tomcircuit/rcl57mcu/hardware/rcl57_mcu/output/ti57mcu_v2_bot3d.png

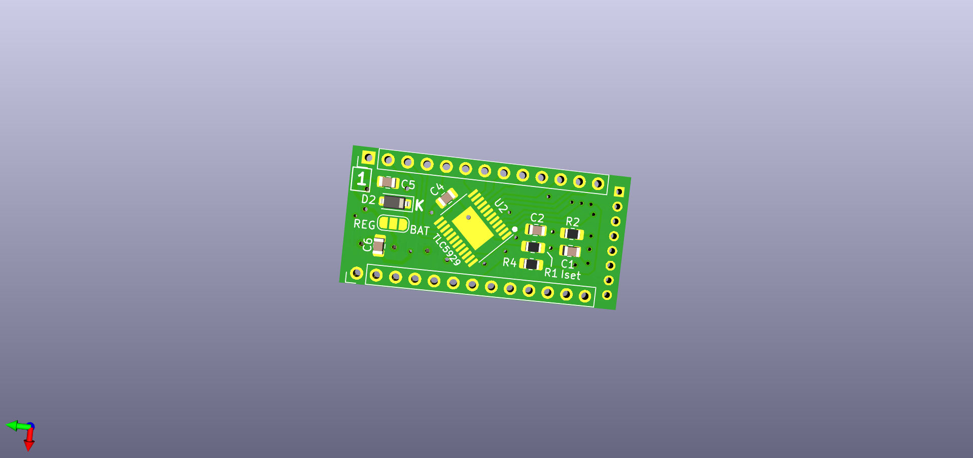
hardware/rcl57_mcu/output/ti57mcu_v2_bot3d.png
