tomcircuit/rcl57mcu/media/column input w 1K8 pulldown segment B.png

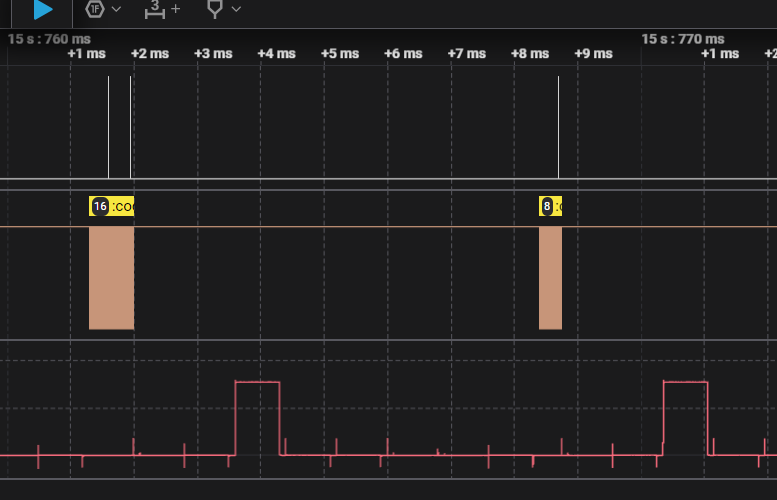
media/column input w 1K8 pulldown segment B.png
