tomcircuit/rcl57mcu/media/column input w 1K8 pulldown segment P.png

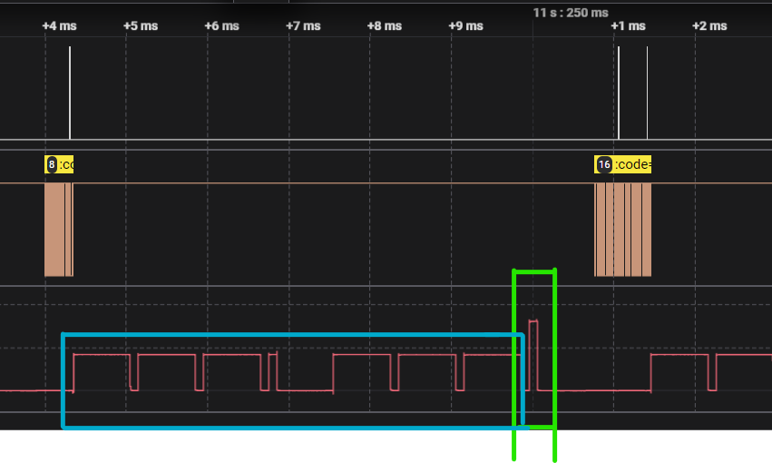
media/column input w 1K8 pulldown segment P.png
