tomcircuit/rcl57mcu/media/connected_segment_pulse.png

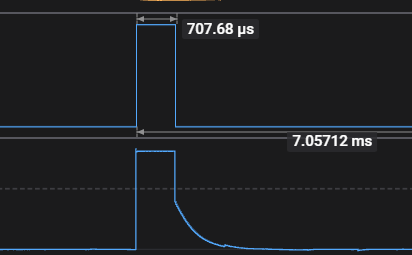
media/connected_segment_pulse.png
