tomcircuit/rcl57mcu/media/first_STM32_emulation_saleae.png

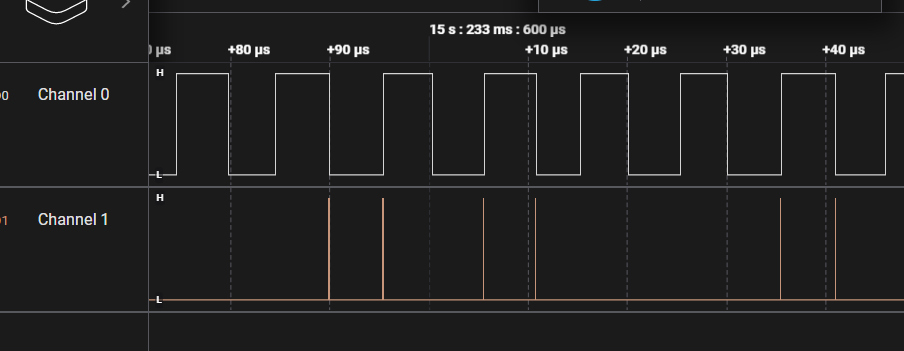
media/first_STM32_emulation_saleae.png
