tomcircuit/rcl57mcu/media/open_segment_pulse.png

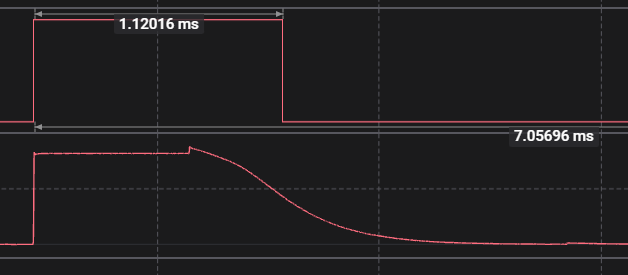
media/open_segment_pulse.png
