tomcircuit/rcl57mcu/media/overlap segments.png

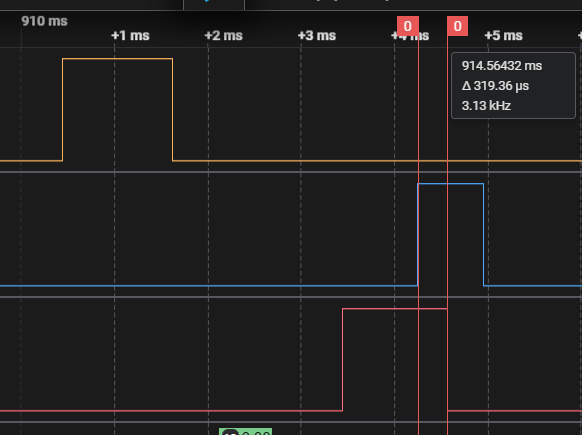
media/overlap segments.png
