tomcircuit/rcl57mcu/media/prototype hack.jpg

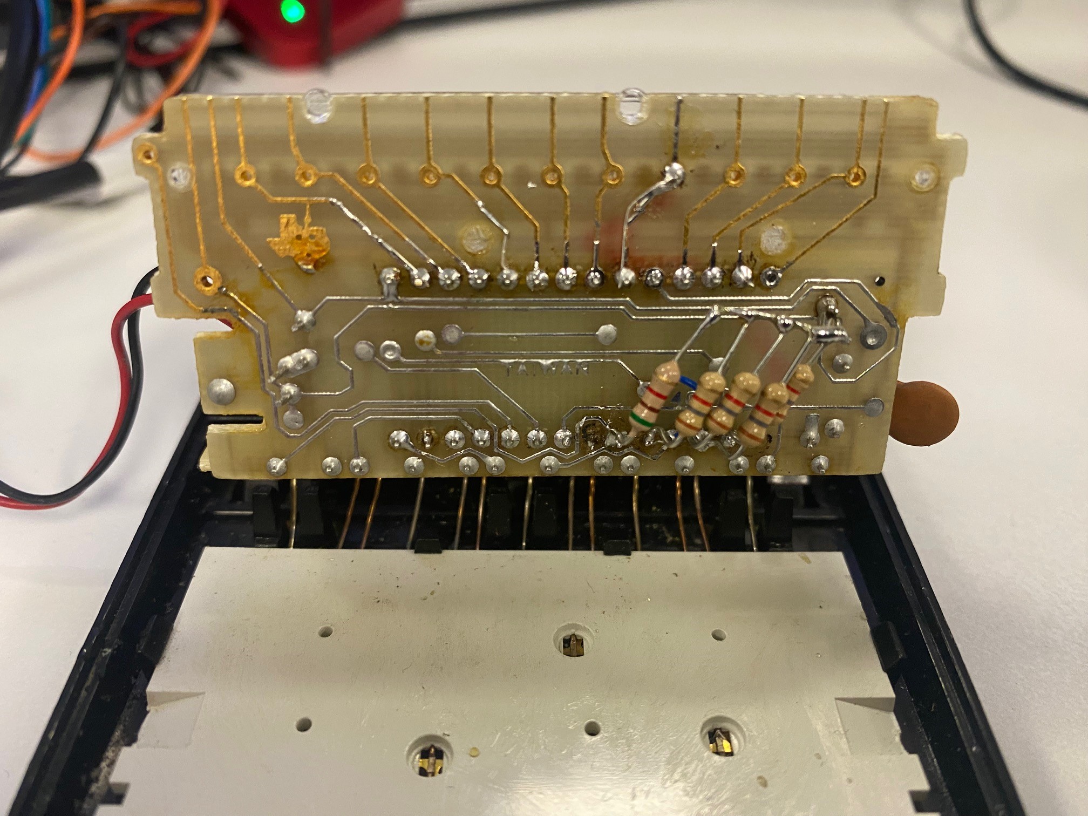
media/prototype hack.jpg
