tomcircuit/rcl57mcu/media/assembled debug board.jpg

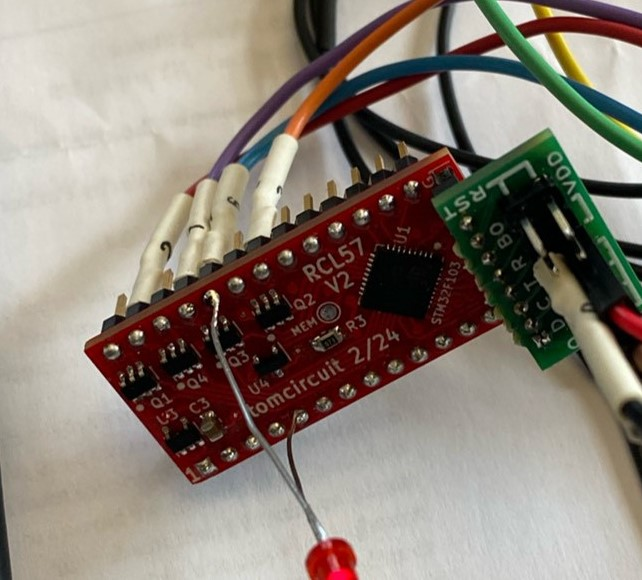
media/assembled debug board.jpg
