tomcircuit/rcl57mcu/hardware/rcl57_mcu/release/fab01/ti57mcu__v1_Assembly.pdf

R Dd10 | +3V3 1 | v tomcircuit CSWCLK | x12 T w10 v1 2024 TMS+ SWDIO | GND | d13 G Q2 U1 C3 Q1 U93 Q4 U96 | U92 D1 U98

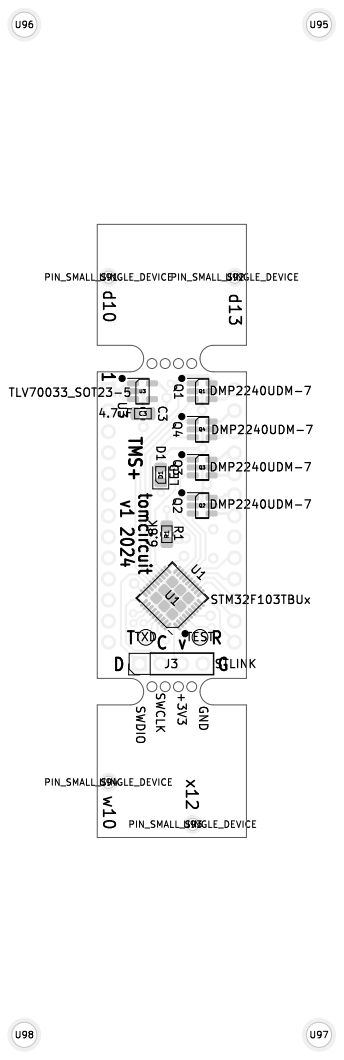
[picture p17: page 1]

Id: 1/1 Title: File: ti57mcu.kicad_pcb Sheet:

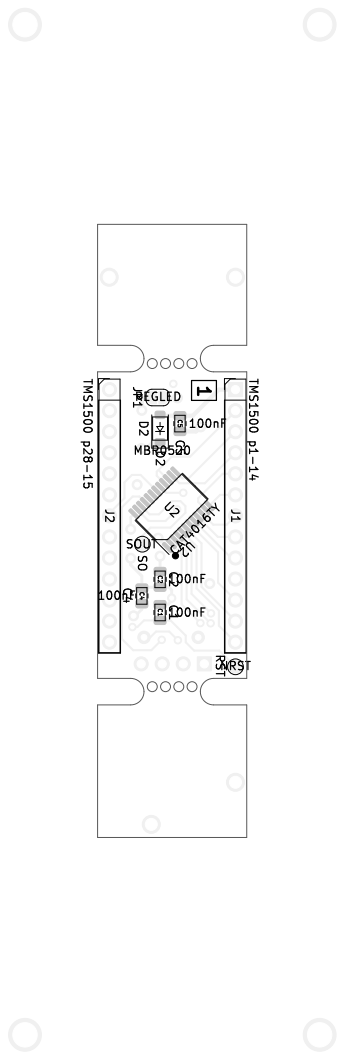
[picture p18: page 2]
Id: 1/1 Title: File: ti57mcu.kicad_pcb Sheet: C²; 100nF MBR0520 D²; 100nF REGLED

1 SO RST C2 D2C5 JP1 C4 U2 C1 1 2 3 4 5 6 1 2 3 4 5 6 ABCD ABCD Date: KiCad E.D.A. kicad 7.0.8 Size: A4 Rev:
