tomcircuit/rcl57mcu/hardware/rcl57_mcu/output/rcl57_mcu_bot_assy.pdf

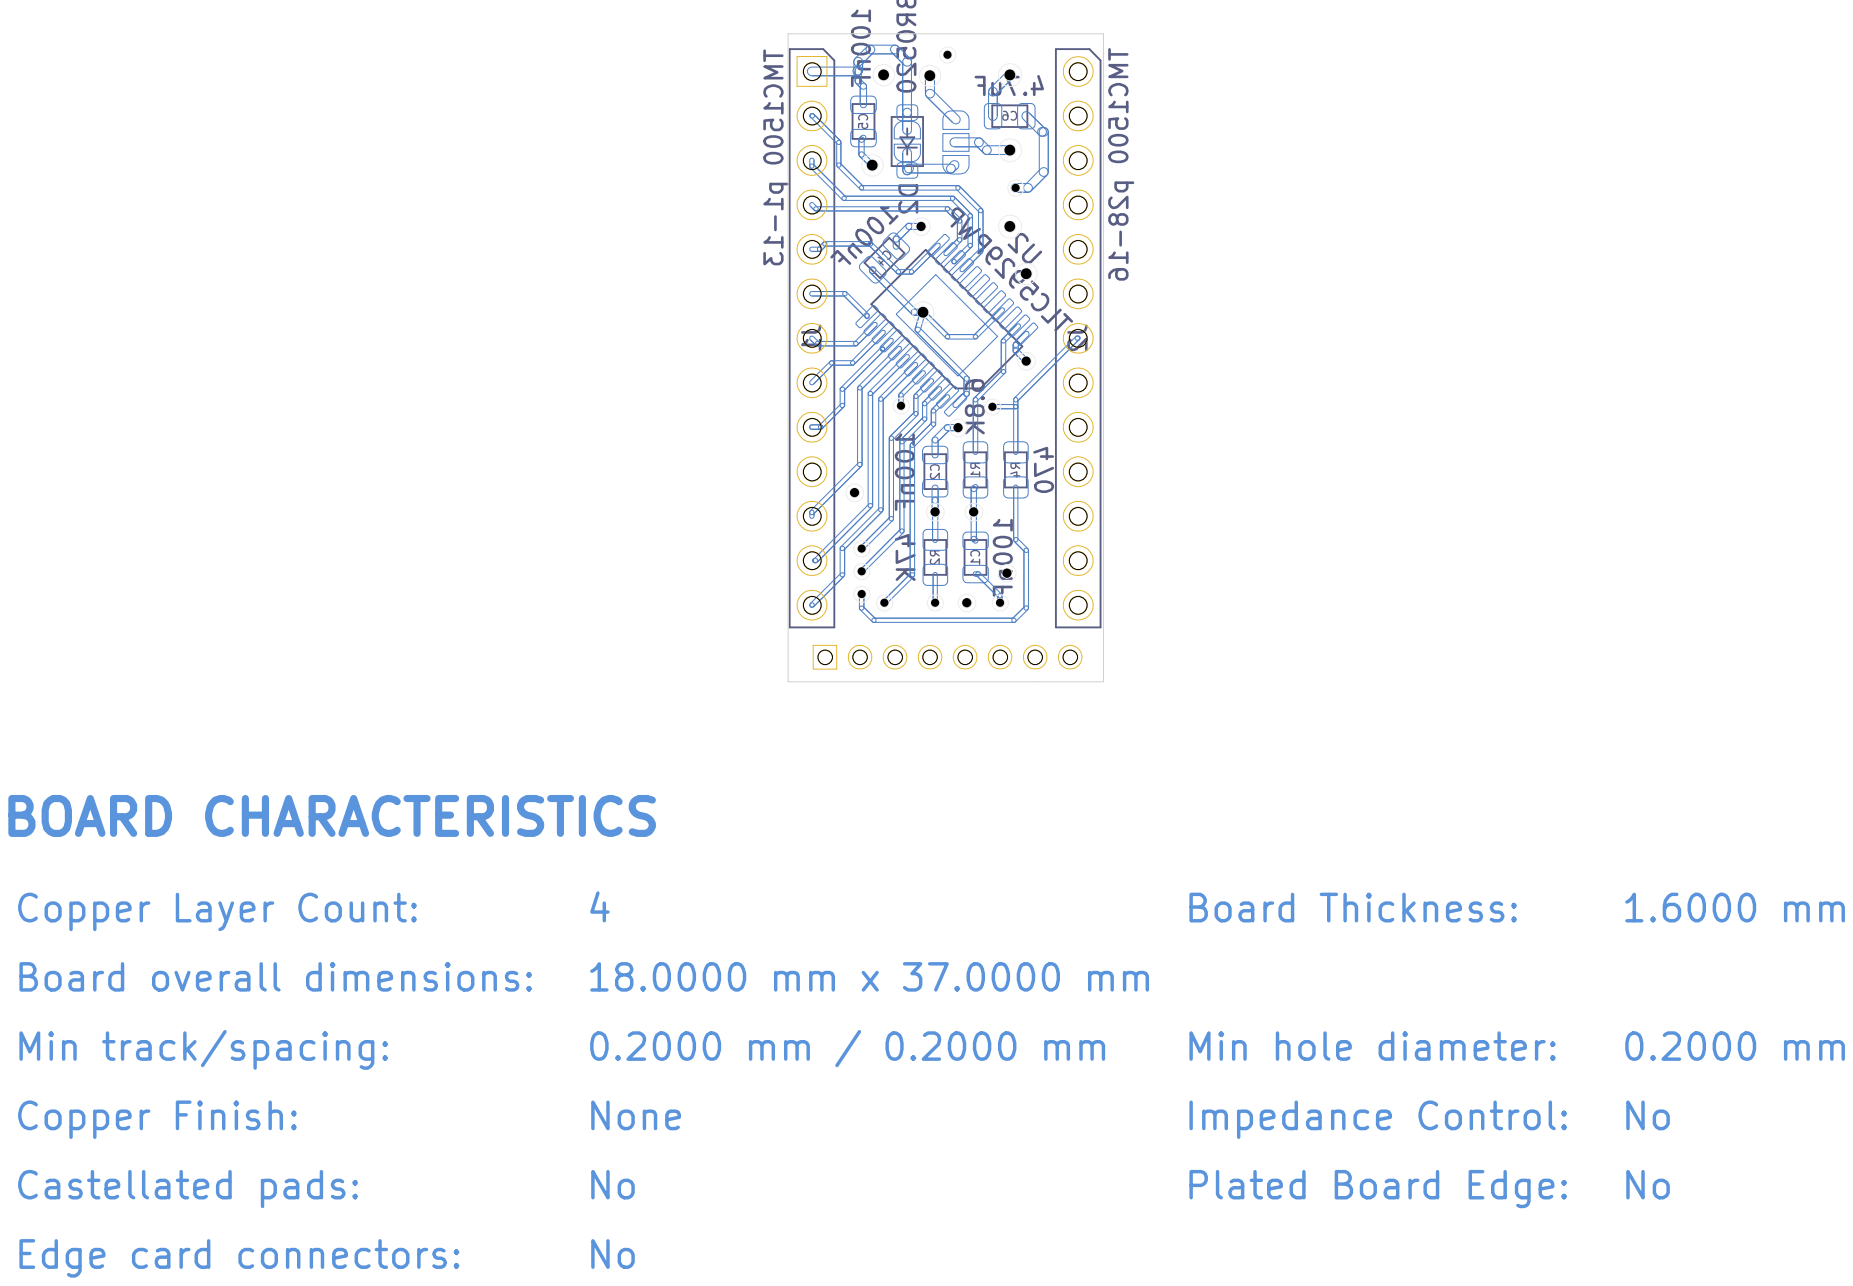
[picture p32: page 1]
