tomcircuit/rcl57mcu/hardware/rcl57_mcu/output/rcl57_mcu_schematic.pdf

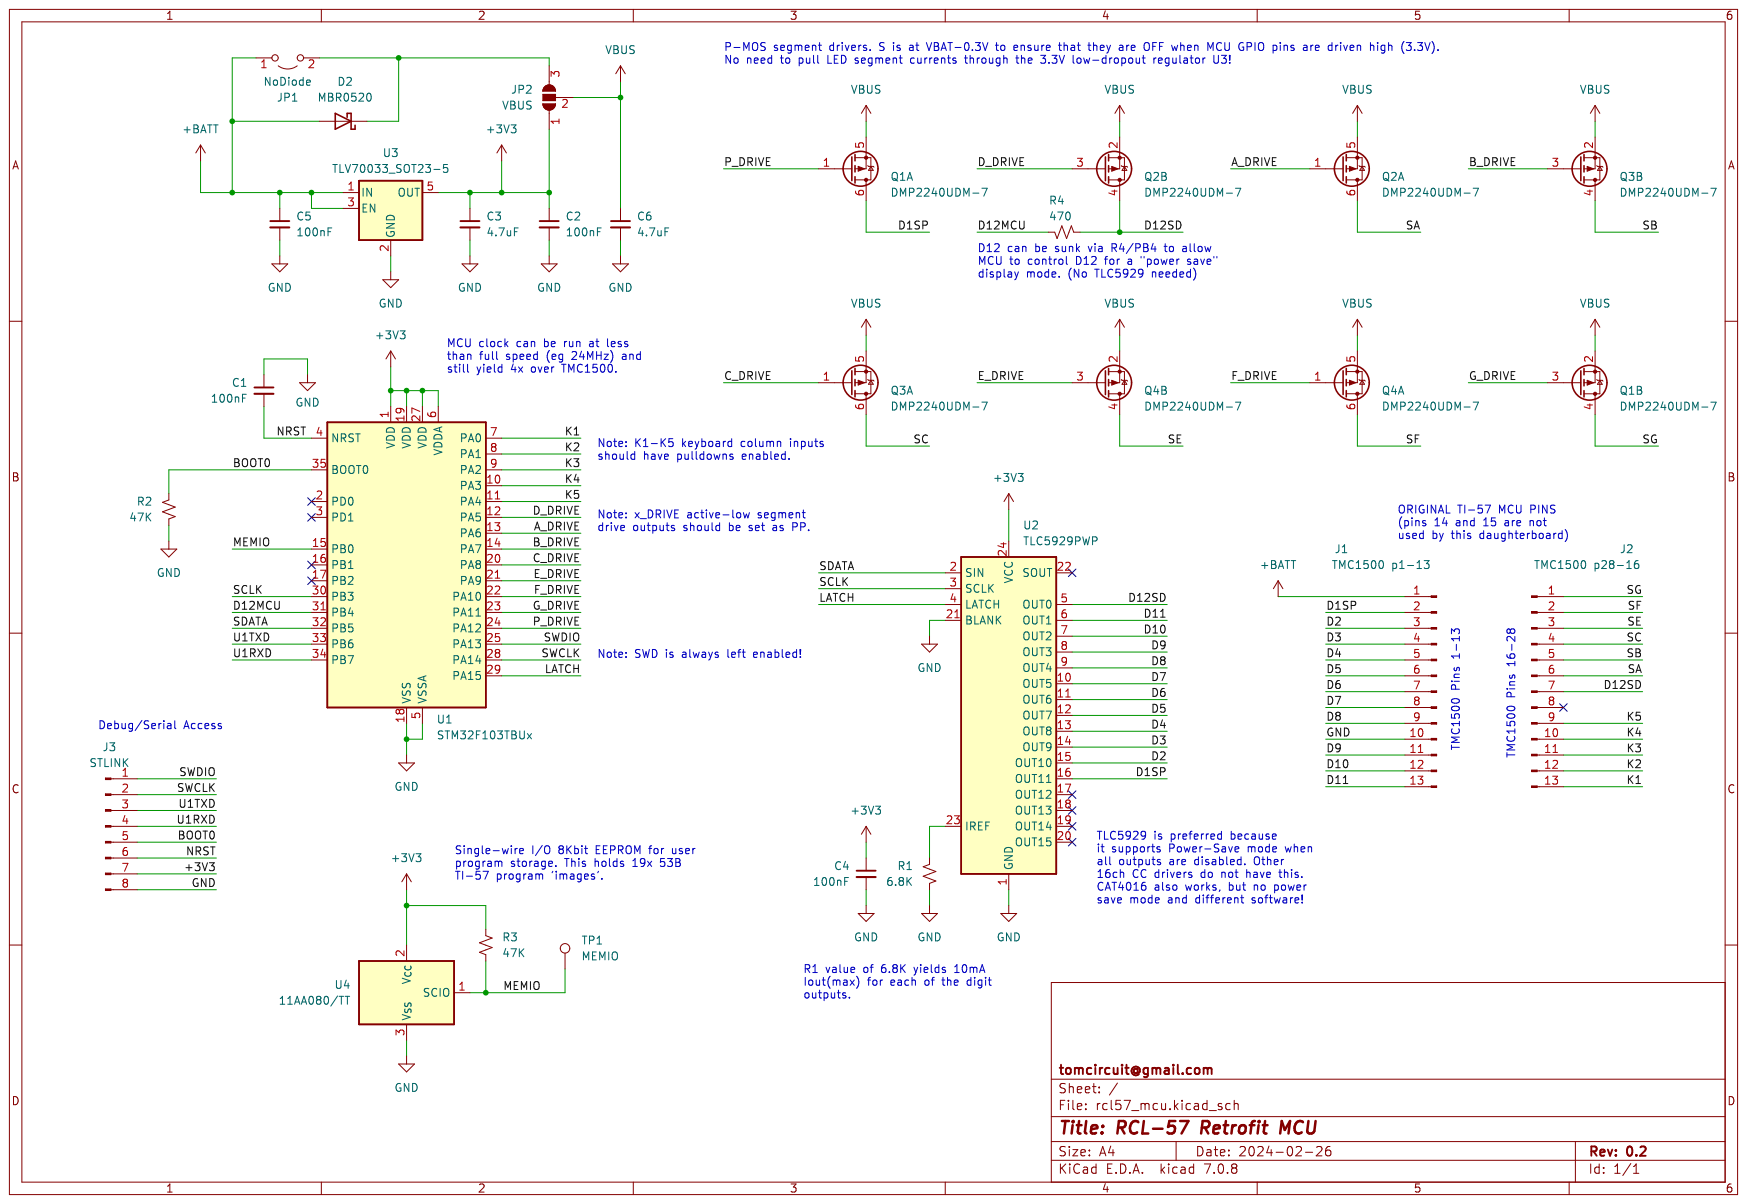
[picture p33: page 1]
