tomcircuit/rcl57mcu/hardware/rcl57_mcu/output/rcl57_mcu_top_assy.pdf

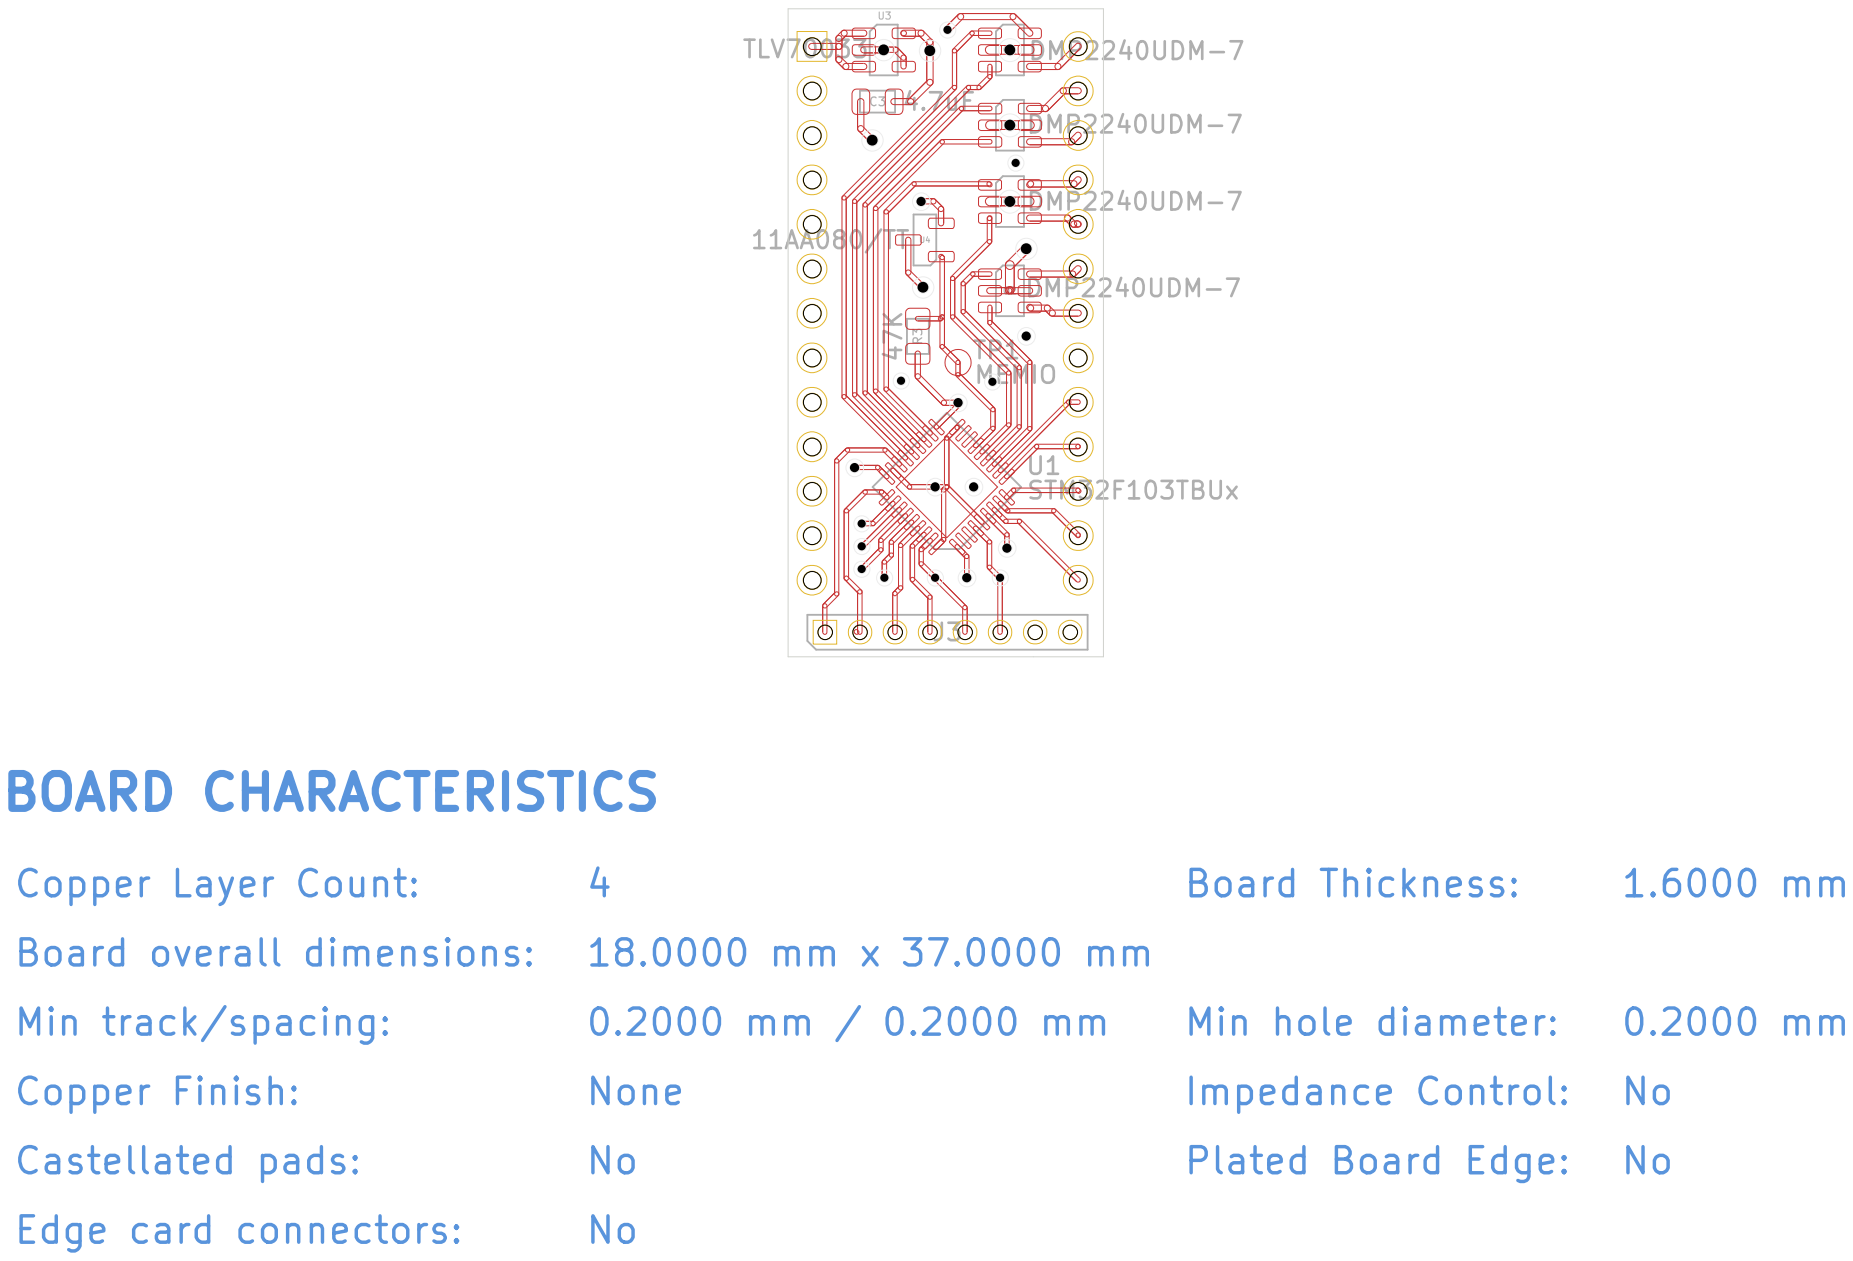
[picture p34: page 1]
