tomcircuit/rcl57mcu/hardware/rcl57_mcu/release/fab01/ti57mcu_v1_schematic.pdf

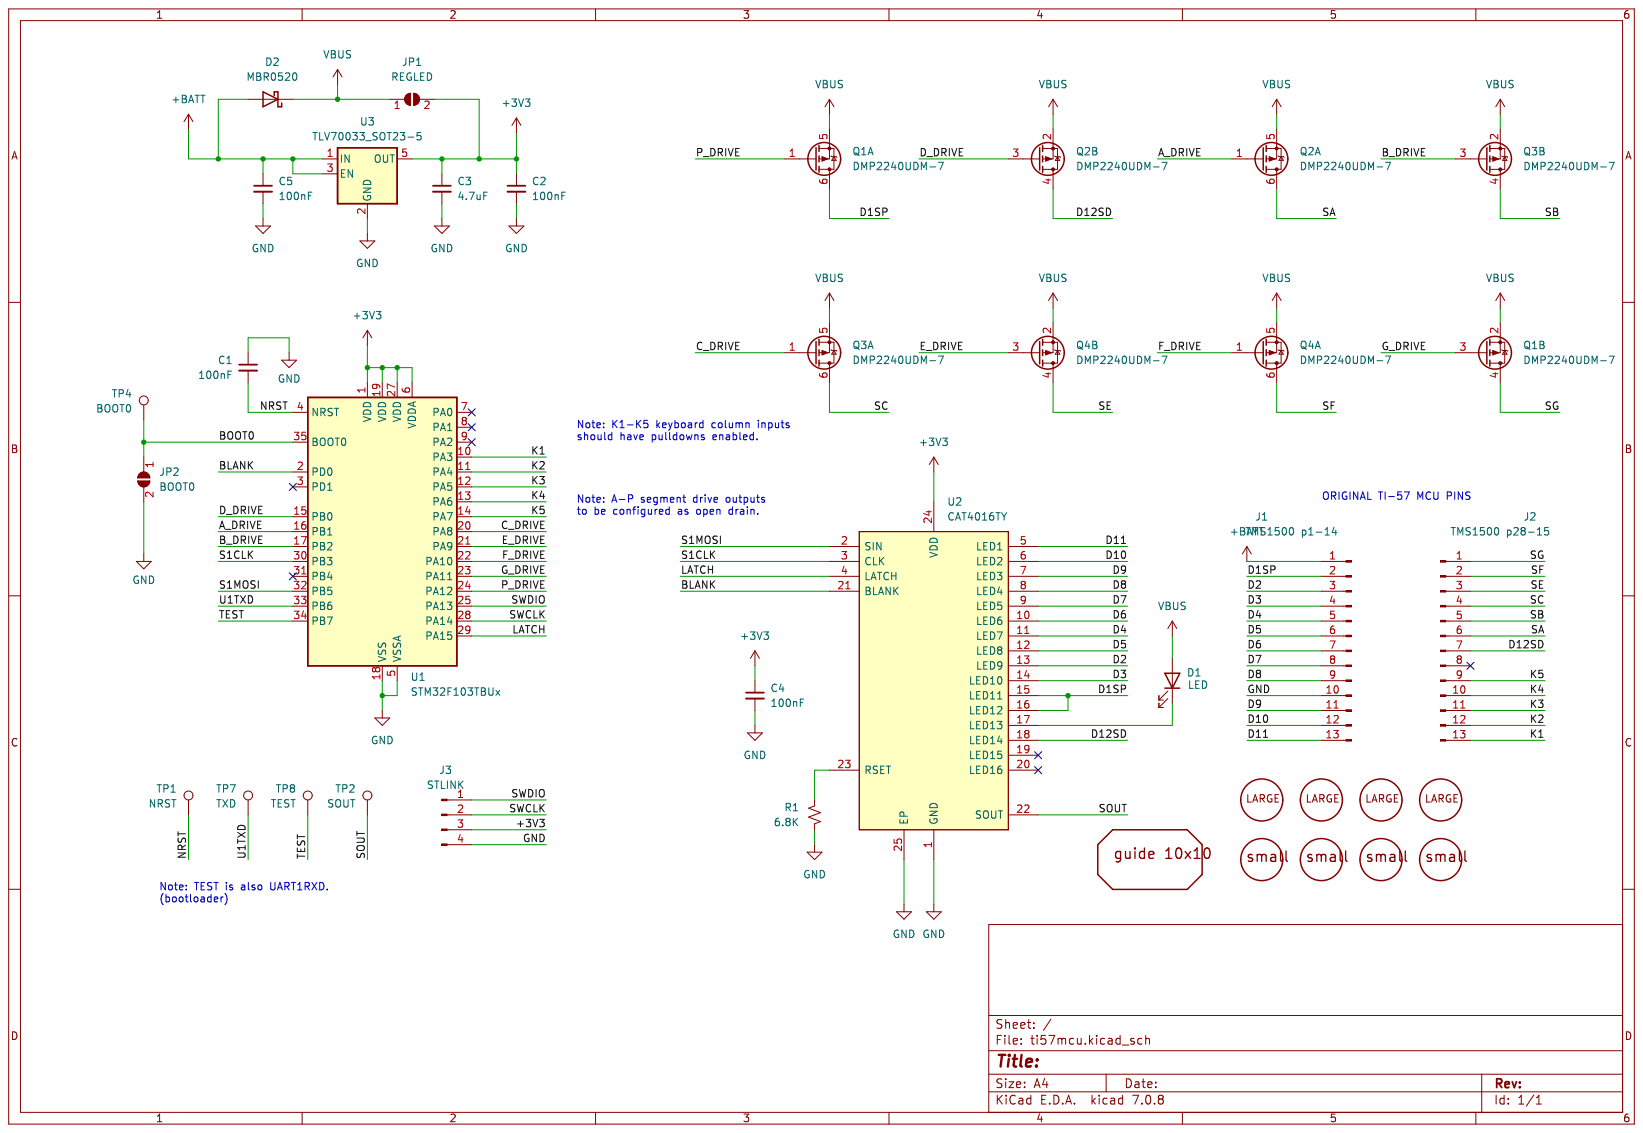
[picture p35: page 1]
