tomcircuit/rcl57mcu/software/ti57mcu/rom55.c

#include "rom55.h"

unsigned short ROM55[] =
{
    4400, 5066, 3089, 6364, 3237, 543, 813, 813, 3233, 6371, 3198, 6266, 3245, 6364, 1991, 5556,
    1865, 103, 3587, 6187, 6815, 3296, 3308, 6290, 6148, 3098, 6578, 2265, 3188, 5365, 6271, 2055,
    3587, 6807, 6257, 6217, 3194, 6154, 3198, 3256, 6364, 3257, 6156, 3194, 6286, 3198, 3193, 7798,
    3184, 6805, 6752, 6221, 3194, 6609, 3240, 6285, 3194, 3879, 6463, 7004, 3252, 6902, 1863, 3589,
    6991, 6809, 6279, 6843, 3194, 7169, 2087, 6603, 6363, 3194, 7864, 4110, 6364, 3194, 7866, 5780,
    6364, 6446, 3096, 6591, 3096, 6573, 3096, 6563, 3194, 6603, 2279, 3198, 7263, 3188, 5164, 3090,
    6242, 3300, 3217, 5136, 3198, 6248, 5164, 6249, 5167, 5136, 3198, 6253, 5167, 3302, 6364, 3088,
    6364, 3194, 3112, 7614, 5167, 5099, 3110, 6644, 5556, 6364, 543, 813, 813, 3495, 3112, 3124,
    6515, 5099, 1887, 2119, 3098, 7694, 6671, 3194, 6283, 5104, 5570, 5768, 6364, 4057, 5099, 1822,
    5989, 6643, 5365, 3194, 3321, 6295, 3320, 3198, 6302, 3304, 3298, 6302, 3194, 7375, 3288, 5174,
    3198, 3194, 7643, 3877, 6619, 3298, 6313, 3322, 7376, 3118, 7361, 2055, 3594, 3584, 1863, 1815,
    1991, 3298, 7371, 3310, 6331, 3322, 6361, 3302, 6360, 3588, 6361, 2271, 3903, 3322, 6344, 5565,
    6345, 3300, 3117, 3112, 2055, 3594, 3589, 6318, 5473, 3584, 1815, 3302, 7667, 3590, 6644, 2079,
    3118, 6355, 3104, 2241, 3585, 3584, 2079, 1879, 3590, 1806, 6364, 3091, 3186, 3233, 3913, 3321,
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
    5679, 3134, 6758, 3133, 3088, 6364, 3194, 6364, 804, 7388, 5104, 6888, 4112, 1991, 5476, 1822,
    4112, 5475, 5564, 5679, 3324, 6728, 5099, 2199, 3090, 2303, 6780, 3188, 5555, 5124, 3237, 5570,
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
};
