tomcircuit/rcl57mcu/software/ti57mcu/rom57.c

#include "rom57.h"

unsigned short ROM57[] = {
    0x120f, 0x1122, 0x13f2, 0x1b8b, 0x0cae, 0x1808, 0x16b5, 0x15fc,
    0x16ad, 0x1b8b, 0x1122, 0x0cae, 0x1ee7, 0x140c, 0x071e, 0x1a8e,
    0x0a28, 0x05d9, 0x198b, 0x1947, 0x19f2, 0x193e, 0x1af3, 0x1b1b,
    0x1a04, 0x0cae, 0x1da3, 0x1124, 0x19f8, 0x1122, 0x1602, 0x1b8b,
    0x1122, 0x163c, 0x1b8b, 0x180a, 0x18f8, 0x0cae, 0x1d0a, 0x1124,
    0x0c72, 0x0c7d, 0x1e4b, 0x0c7a, 0x1f8a, 0x0da7, 0x0c70, 0x1a4b,
    0x0fe1, 0x1a77, 0x189c, 0x1aed, 0x18b7, 0x0cae, 0x1c69, 0x1122,
    0x1a70, 0x1124, 0x0cae, 0x1fb6, 0x0c72, 0x1e27, 0x0f27, 0x1a1e,
    0x0827, 0x185c, 0x187a, 0x1aea, 0x18b8, 0x1122, 0x0cae, 0x1c95,
    0x1840, 0x1124, 0x0cae, 0x1fcc, 0x0c72, 0x1e51, 0x0c93, 0x1a57,
    0x0cbd, 0x1a8f, 0x1a17, 0x1af0, 0x1a63, 0x0cd8, 0x1860, 0x0cd8,
    0x18a7, 0x1122, 0x0cae, 0x1fcd, 0x0ca6, 0x1a91, 0x0c74, 0x1a7e,
    0x0c28, 0x0cae, 0x1a6a, 0x0cda, 0x0ce0, 0x18aa, 0x1122, 0x0c91,
    0x1b8a, 0x0cb2, 0x186d, 0x0c7a, 0x19a5, 0x1122, 0x18f9, 0x081f,
    0x08c1, 0x140d, 0x081f, 0x0757, 0x0e04, 0x070e, 0x1b8b, 0x13e2,
    0x0d01, 0x1b8b, 0x1124, 0x0cae, 0x1c84, 0x0c75, 0x0c72, 0x1e1e,
    0x0cb2, 0x0ca5, 0x1b8f, 0x0e03, 0x140c, 0x0701, 0x0c7a, 0x18b5,
    0x13f8, 0x08e0, 0x08e0, 0x0cee, 0x1890, 0x0e00, 0x0701, 0x0e06,
    0x08e1, 0x0e0a, 0x0cee, 0x1e17, 0x1885, 0x15af, 0x1587, 0x0c7a,
    0x1f8b, 0x075f, 0x15d3, 0x1b8b, 0x1122, 0x0c7a, 0x1c04, 0x1668,
    0x0cae, 0x1b8b, 0x0324, 0x1f8b, 0x16b5, 0x1603, 0x1b8b, 0x0c24,
    0x0cae, 0x1a6a, 0x0d1f, 0x1124, 0x140c, 0x0c39, 0x0c3d, 0x0ce2,
    0x1cb5, 0x0c38, 0x0cda, 0x1cb5, 0x0c3c, 0x1472, 0x1b8f, 0x0cec,
    0x0cb2, 0x1da6, 0x1122, 0x1532, 0x0cae, 0x18bf, 0x0ca0, 0x0c7a,
    0x18c6, 0x0ce8, 0x0ce2, 0x18c6, 0x0cae, 0x1c6f, 0x08df, 0x0dff,
    0x149c, 0x0e08, 0x0ddf, 0x08ff, 0x0f25, 0x1a77, 0x0ce2, 0x18d2,
    0x0ca2, 0x1c70, 0x0c2e, 0x1e77, 0x0820, 0x0c2a, 0x18dd, 0x0c2e,
    0x1cdd, 0x0c26, 0x0c24, 0x18df, 0x0c23, 0x0c2b, 0x0ce4, 0x0807,
    0x0e0a, 0x1412, 0x0717, 0x07c7, 0x0ce2, 0x1cf6, 0x0cee, 0x18ec,
    0x0ca2, 0x1875, 0x146e, 0x1875, 0x0cea, 0x0c39, 0x18f0, 0x0c38,
    0x0ca2, 0x18f4, 0x1604, 0x18f5, 0x15d1, 0x1412, 0x146d, 0x1a8f,
    0x0cae, 0x0ce0, 0x18b7, 0x1080, 0x1400, 0x1410, 0x0a0d, 0x1906,
    0x0a61, 0x1416, 0x0a60, 0x1423, 0x0a61, 0x18fd, 0x0ad9, 0x1423,
    0x194b, 0x1461, 0x1080, 0x1403, 0x0a27, 0x0c30, 0x0c34, 0x0a45,
    0x1906, 0x0a60, 0x1416, 0x0a61, 0x1423, 0x0a60, 0x190c, 0x0c72,
    0x0e08, 0x191b, 0x1442, 0x0c99, 0x0717, 0x15a1, 0x0f4f, 0x0e03,
    0x0cae, 0x1937, 0x0cb2, 0x1917, 0x0cb2, 0x0ca5, 0x191f, 0x0ca1,
    0x05e1, 0x0a3f, 0x0c7a, 0x192d, 0x0c2c, 0x0cae, 0x1932, 0x0f67,
    0x0c78, 0x0f08, 0x0ac7, 0x1403, 0x1423, 0x0ca2, 0x1d4b, 0x0ca1,
    0x1400, 0x1410, 0x0a0d, 0x1a16, 0x0a20, 0x1945, 0x1080, 0x0cae,
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
};
